edwindertien/InteractiveAudioplayer/ESP32bodyBridge/src/main.cpp

#include <Arduino.h>
#include "Config.h"
#include "EspNow.h"
#include "StatusLed.h"
#include "PairButton.h"
#include "Cli.h"

void setup() {
    setCpuFrequencyMhz(80);
    Serial.begin(115200);
    delay(300);
    Serial.println("\n=== Body Bridge ===");

    teensySetup();     // defined in EspNow.h
    statusLedSetup();
    espNowSetup();
    pairButtonSetup();

    Serial.println("Waiting for hand unit...");
    printHelp();
}

uint32_t streamTimer    = 0;
uint32_t heartbeatTimer = 0;

void loop() {
    uint32_t now = millis();
    cliPoll();
    pairButtonUpdate(now);
    statusLedUpdate(now, handPaired, lastRxMs, pairingMode);

    // Heartbeat to hand unit every 1s
    if (now - heartbeatTimer >= 1000) {
        heartbeatTimer = now;
        espNowSendHeartbeat();
    }

    // Proximity stream to terminal (toggled via 'stream' command)
    if (streamProx && lastRxMs > 0 && (millis() - streamTimer >= 100)) {
        streamTimer = millis();
        uint8_t bars = (uint8_t)map(constrain(lastDist, 0, 500), 0, 500, 30, 0);
        char bar[32] = {}; memset(bar, '#', bars);
        Serial.printf("[PROX]  %4u mm  %s  touch:%u\n",
                      lastDist, bar, lastTouch);
    }

    vTaskDelay(pdMS_TO_TICKS(1));
}
